kdcgarber/TRS-80-M1-Keyboard-Keys/images/AllOnPlate.jpg

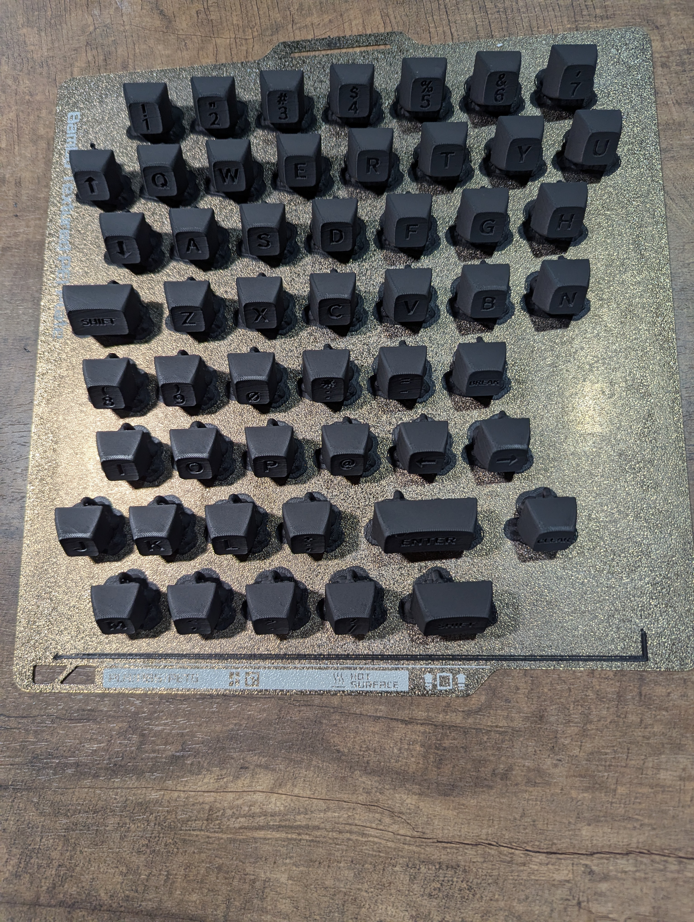
images/AllOnPlate.jpg
