kdcgarber/TRS-80-M1-Keyboard-Keys/images/EnterKeycap.jpg

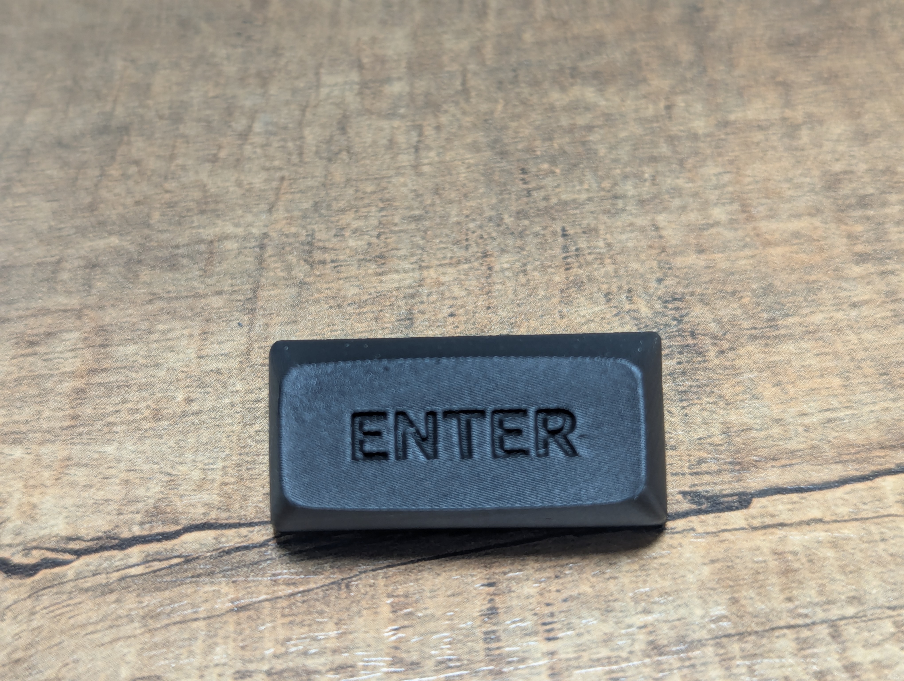
images/EnterKeycap.jpg
