kdcgarber/TRS-80-M1-Keyboard-Keys/images/flatSample.jpg

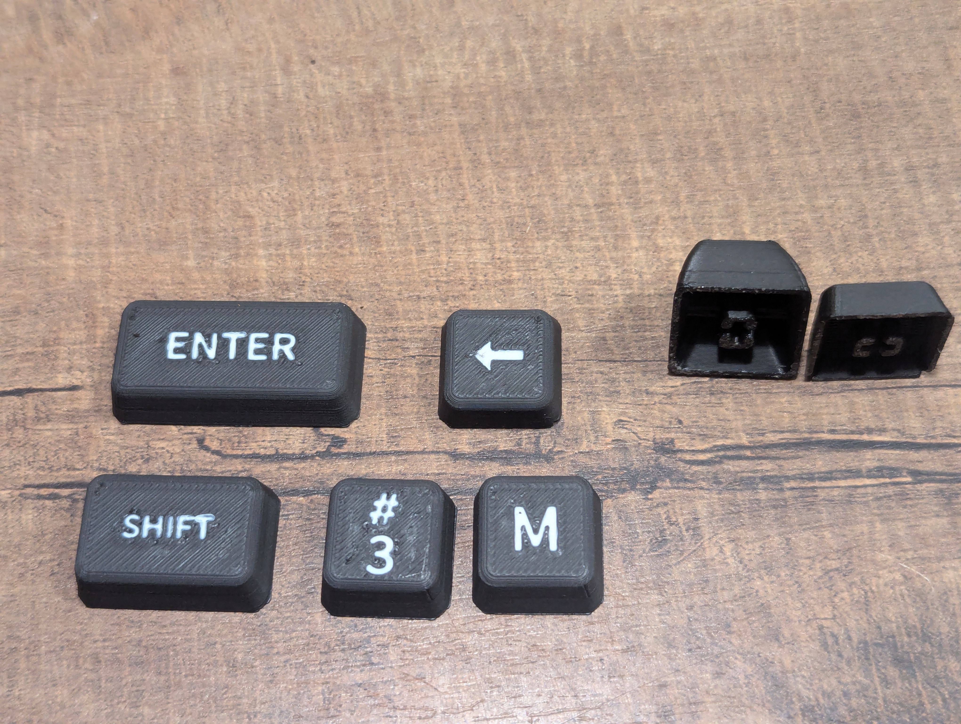
images/flatSample.jpg
