kdcgarber/TRS-80-M1-Keyboard-Keys/images/m1keys-offplate.jpg

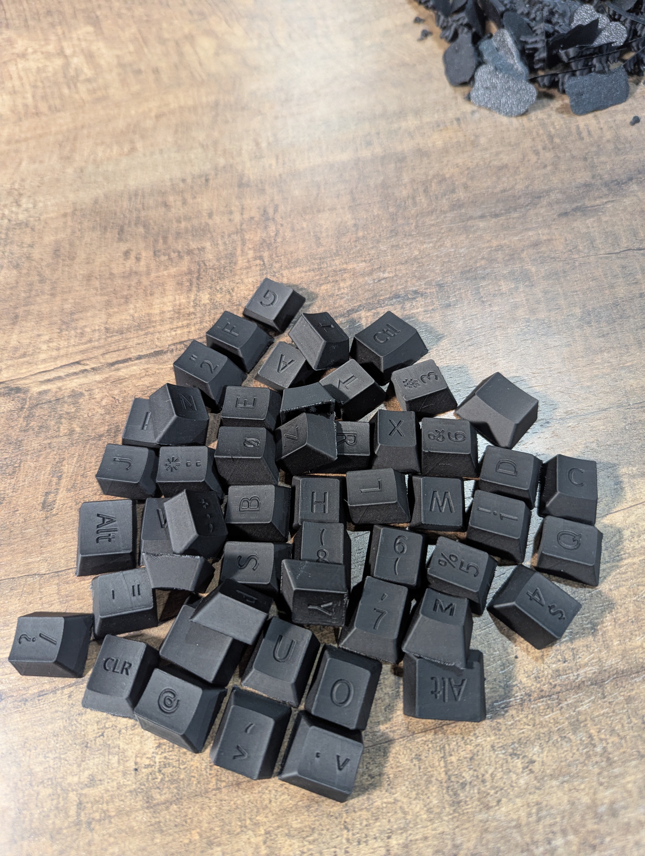
images/m1keys-offplate.jpg
