kdcgarber/TRS-80-M1-Keyboard-Keys/images/m1keys-partial.jpg

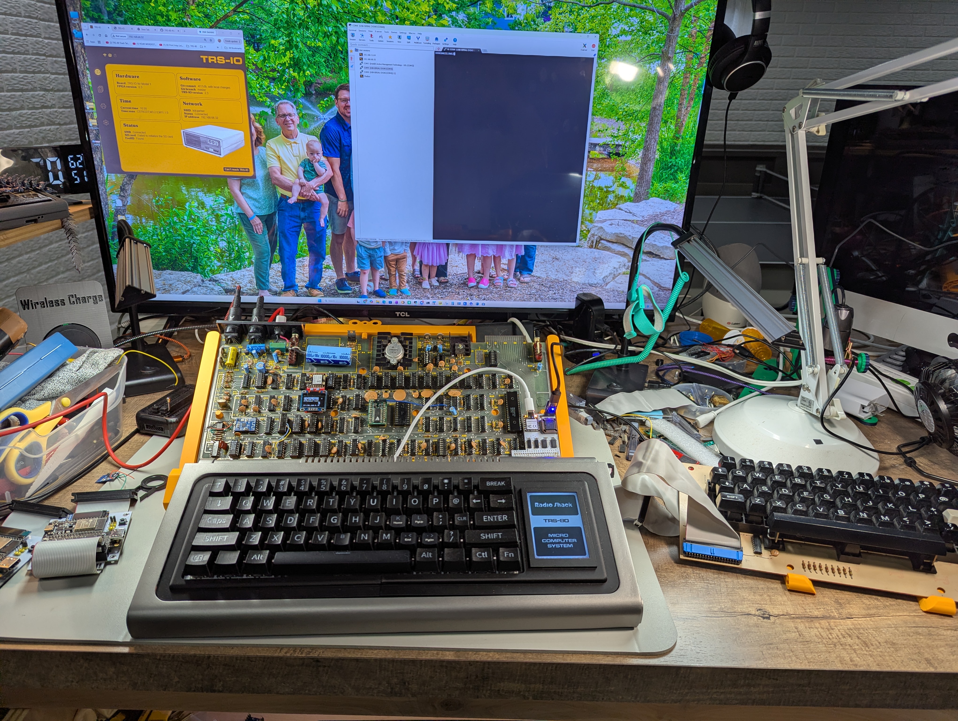
images/m1keys-partial.jpg
