kdcgarber/TRS-80-M1-Keyboard-Keys/images/m1keys-usb2.jpg

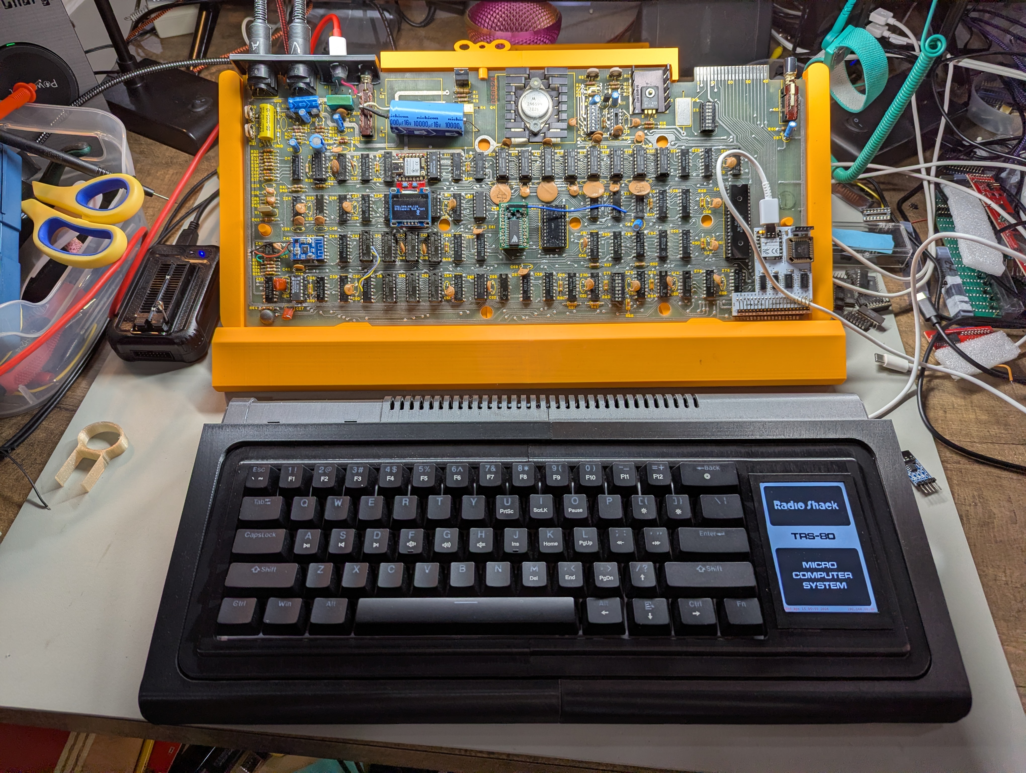
images/m1keys-usb2.jpg
