kdcgarber/TRS-80-M1-Keyboard-Keys/images/OpenSCADView.png

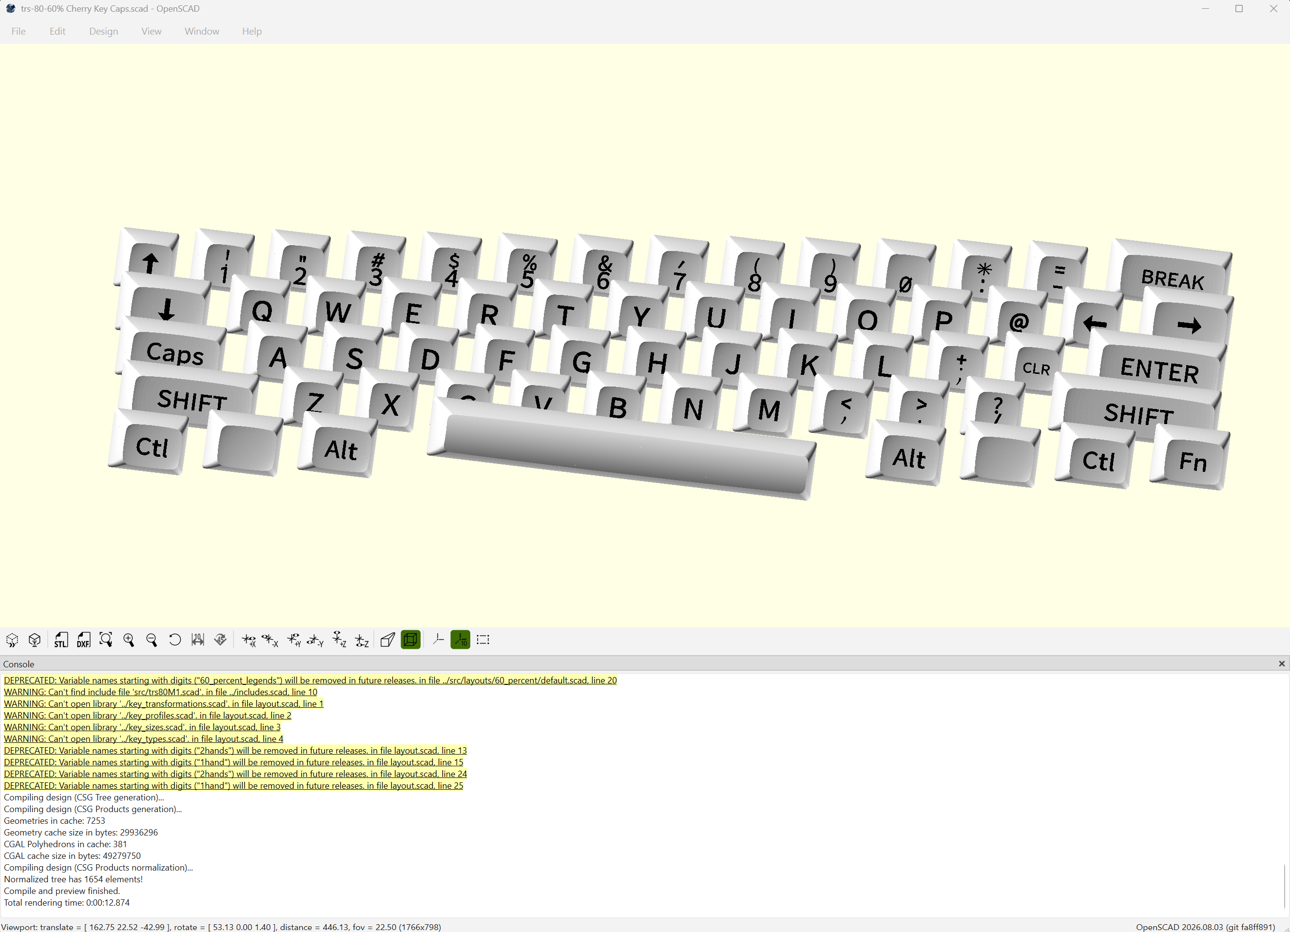
images/OpenSCADView.png
