kdcgarber/TRS-80-M1-Keyboard-Keys/images/Waste.jpg

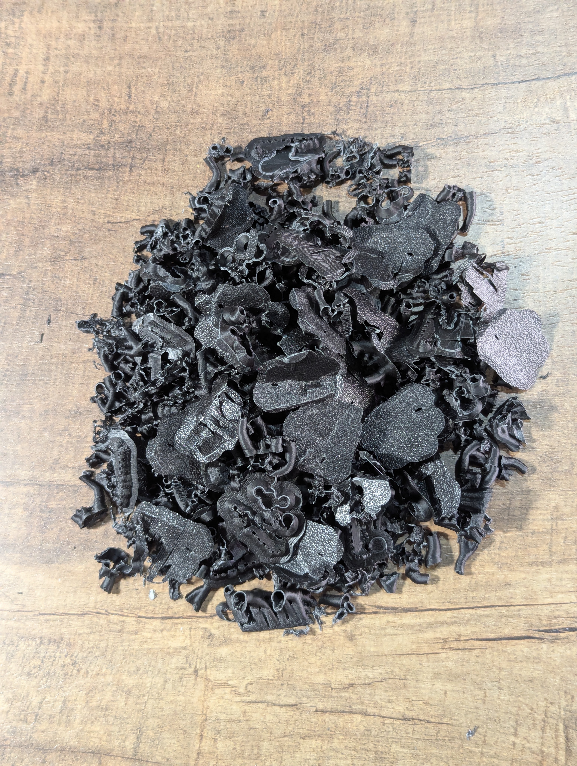
images/Waste.jpg
