kdcgarber/TRS-80-M1-Keyboard-Keys/images/withLid.jpg

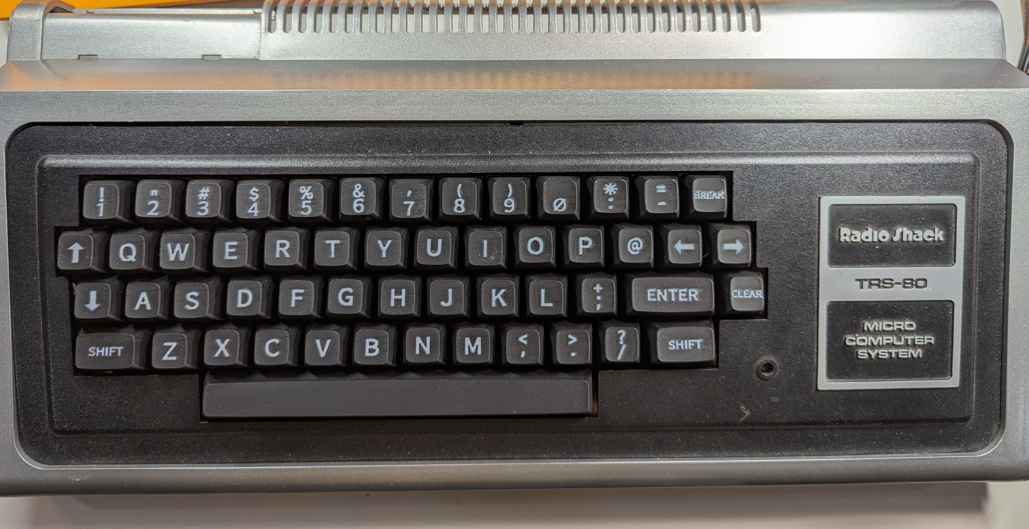
images/withLid.jpg
