kdcgarber/TRS-80-M1-Keyboard-Keys/openscad/KeyV2-All/TRS-80-1978-M1-noLetters/flat.stl

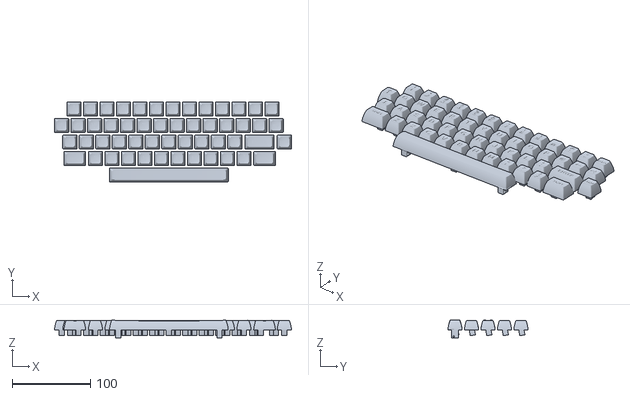
[picture p43: CAD file, 2026-09-26]
openscad/KeyV2-All/TRS-80-1978-M1-noLetters/flat.stl
302.4 x 102.4 x 22.9
