kdcgarber/TRS-80-M1-Keyboard-Keys/openscad/KeyV2-All/TRS-80-1978-M1/trs-80-1978-KeyCaps.3mf

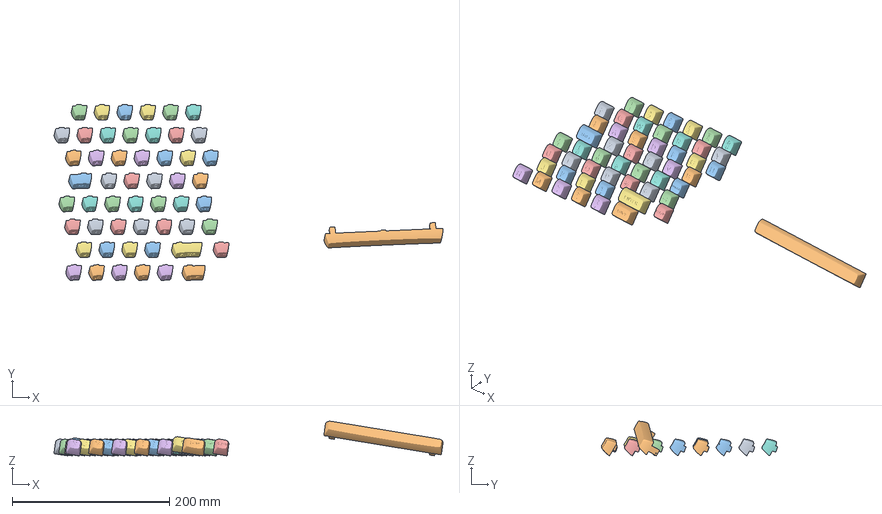
[picture p44: CAD file, 2026-09-26]
openscad/KeyV2-All/TRS-80-1978-M1/trs-80-1978-KeyCaps.3mf
494.4 x 223.9 x 44.1 mm
