kdcgarber/TRS-80-M1-Keyboard-Keys/openscad/KeyV2-All/src/features/legends.scad

module keytext(text, position, font_size, font_face, depth) {
  woffset = (top_total_key_width()/3.5) * position[0];
  hoffset = (top_total_key_height()/3.5) * -position[1];
  translate([woffset, hoffset, -depth]){
    color($legend_color) linear_extrude(height=$dish_depth + depth){
      text(text=text, font=font_face, size=font_size, halign="center", valign="center");
    }
  }
}

module legends(depth=0) {
  if (len($front_legends) > 0) {
    front_of_key() {
      for (i=[0:len($front_legends)-1]) {
        rotate([90,0,0]) keytext($front_legends[i][0], $front_legends[i][1], $front_legends[i][2], $front_legends[i][3], depth);
  	  }
    }
  }
  if (len($legends) > 0) {
    top_of_key() {
      for (i=[0:len($legends)-1]) {
        keytext($legends[i][0], $legends[i][1], $legends[i][2], $legends[i][3], depth);
      }
    }
  }
}
