kdcgarber/TRS-80-M1-Keyboard-Keys/openscad/KeyV2-All/includes.scad

use <src/key.scad>

include <src/settings.scad>
include <src/key_sizes.scad>
include <src/key_profiles.scad>
include <src/key_types.scad>
include <src/key_transformations.scad>
include <src/key_helpers.scad>
include <src/key_layouts.scad>
include <src/trs80M1.scad>
