kdcgarber/TRS-80-M1-Keyboard-Keys/openscad/KeyV2-All/src/supports.scad

include <supports/flared.scad>
include <supports/flat.scad>
include <supports/bars.scad>
include <supports/trs801978M1bars.scad>

module supports(type, stem_type, loft, height) {
  if (type == "flared") {
    flared(stem_type, loft, height);
  } else if (type == "flat") {
    flat(stem_type, loft, height);
  } else if (type == "bars") {
    bars(stem_type, loft, height);
  } else if (type == "trs801978M1bars") {
    trs801978M1bars(stem_type, loft, height);
  } else if (type == "disable") {
    children();
  } else {
    echo("Warning: unsupported $support_type");
  }
}
