kdcgarber/TRS-80-M1-Keyboard-Keys/images/trs-80-1978-KeyCaps2ColorSliceResults.png

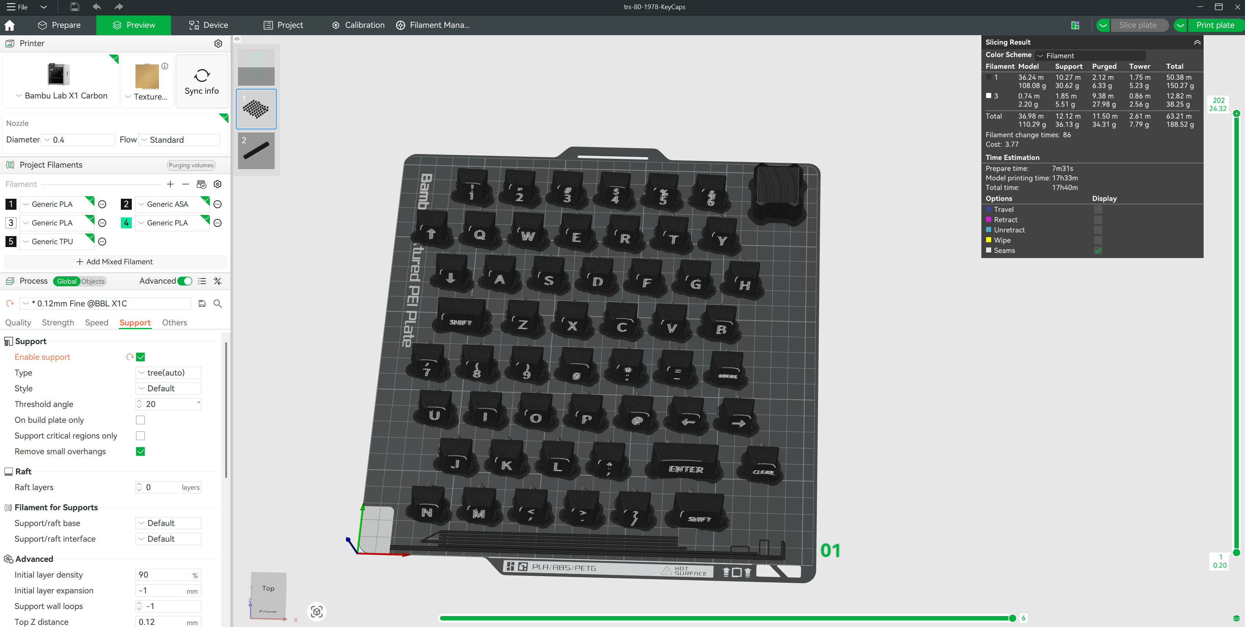
images/trs-80-1978-KeyCaps2ColorSliceResults.png
